kt314-sh/MTL-01-01/03-pic/IMG_20260615_190755_317.jpg

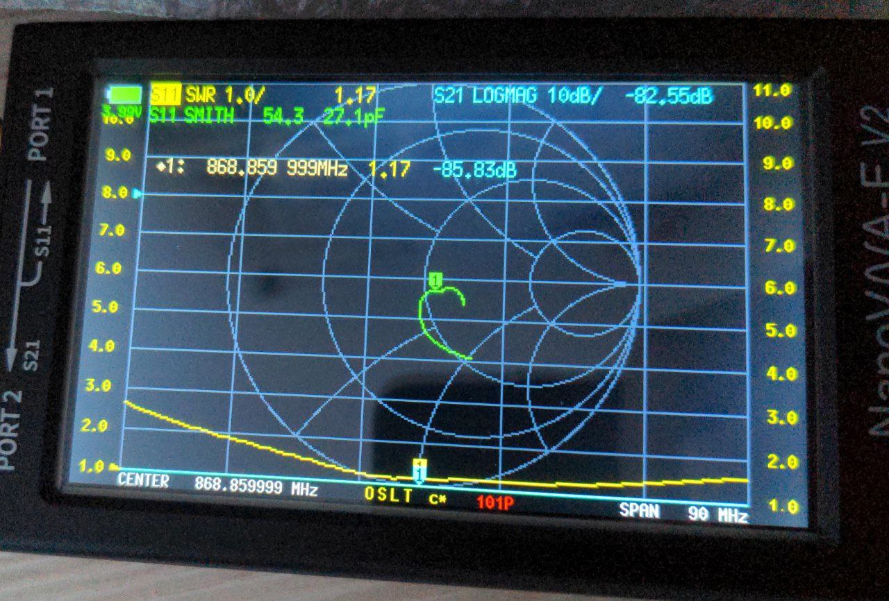
03-pic/IMG_20260615_190755_317.jpg
