kt314-sh/MTL-01-01/03-pic/MTL-01.jpg

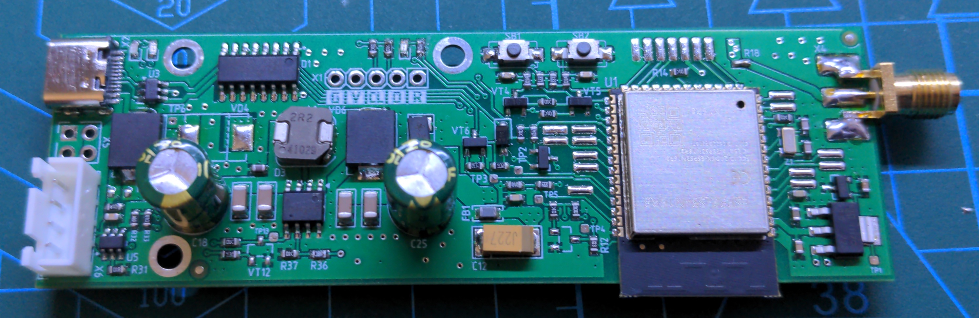
03-pic/MTL-01.jpg
