kt314-sh/MTL-01-01/03-pic/MTL-var.2-t.jpg

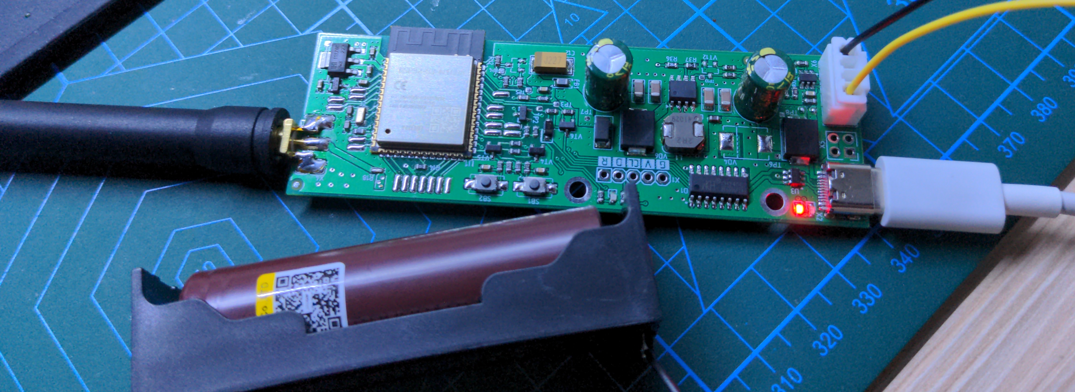
03-pic/MTL-var.2-t.jpg
